BYU-I-eBadge/byu-i-ebadge.github.io/minibadge_examples/I2C/i2c_flash_minibadge.kicad_sch

## KiCad design minibadge_examples/I2C/i2c_flash_minibadge.kicad_sch (2025-11-24)

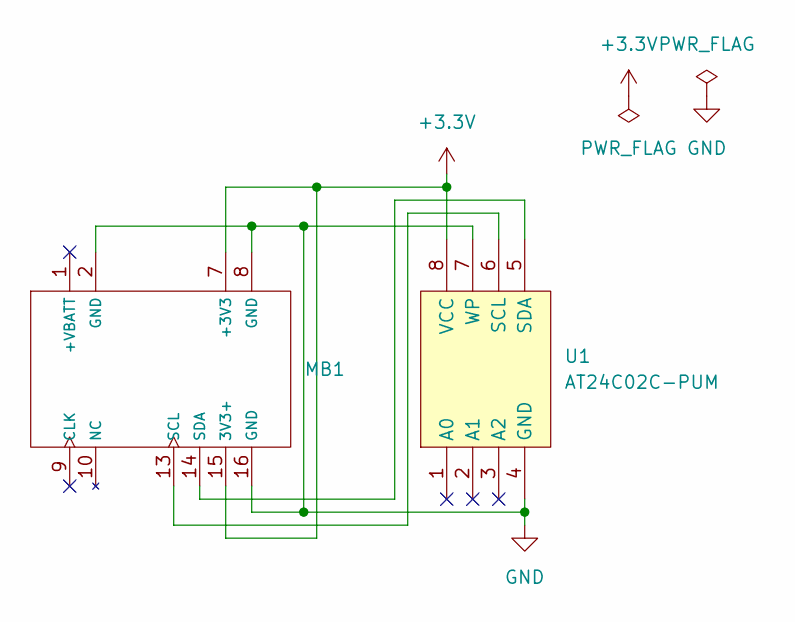
[picture p73: schematic i2c_flash_minibadge.kicad_sch]

Parts:
MB1: MiniBadge_Full
U1: AT24C02C-PUM; DIP-8_L10.0-W6.5-P2.54-LS7.6-BL-A; LCSC Part C8810

Connections:
+3.3V: MB1.7 (+3V3), MB1.15 (3V3+), U1.8 (VCC)
GND: MB1.2 (GND), MB1.8 (GND), MB1.16 (GND), U1.4 (GND), U1.7 (WP)
unnamed: MB1.13 (SCL), U1.6 (SCL)
unnamed: MB1.14 (SDA), U1.5 (SDA)
